whowechina/popn_pico/PCB/Popn2/3dmodels/SKSTAAE010.stp

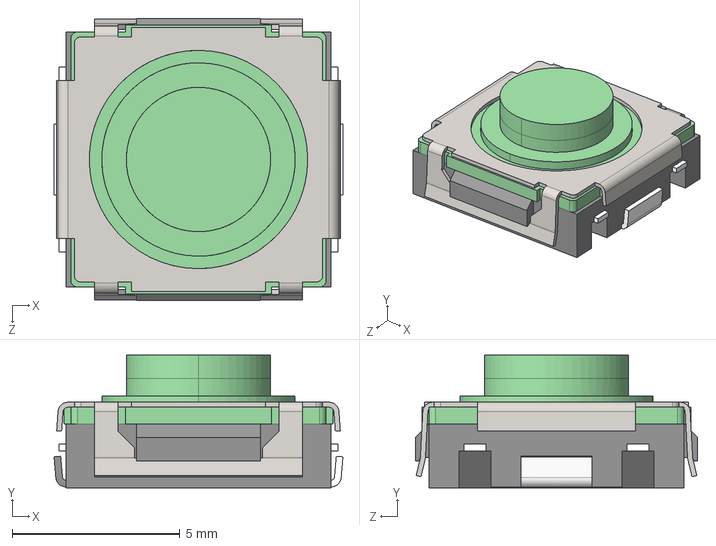
[picture p54: CAD file, 2024-12-04]
PCB/Popn2/3dmodels/SKSTAAE010.stp
8.61 x 3.95 x 8.40 mm
