whowechina/popn_pico/Production/3DPrint/popn_pico2_support.stl

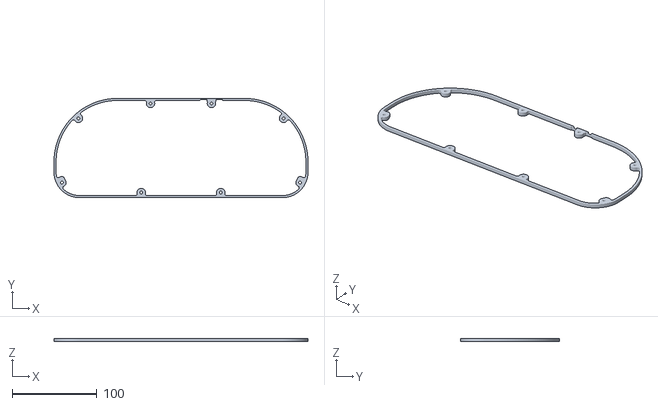
[picture p55: CAD file, 2025-01-06]
Production/3DPrint/popn_pico2_support.stl
300.3 x 117.3 x 4.00
