whowechina/popn_pico/PCB/Popn2/3dmodels/SPEAKER_SMD_1340.STEP

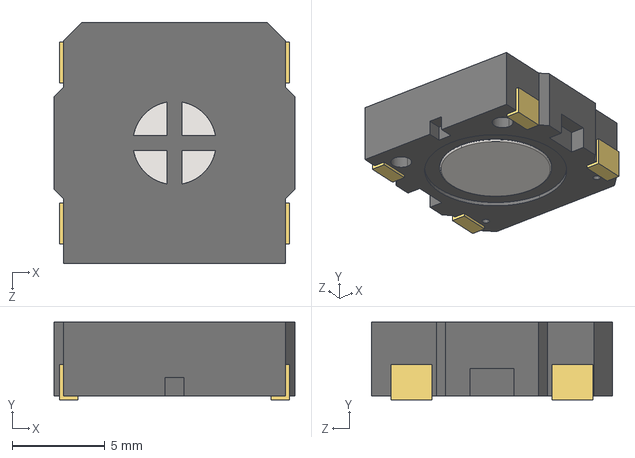
[picture p56: CAD file, 2024-12-04]
PCB/Popn2/3dmodels/SPEAKER_SMD_1340.STEP
13.0 x 4.20 x 13.0 mm
