whowechina/popn_pico/PCB/Popn2/3dmodels/User Library-WS2812-2020.step

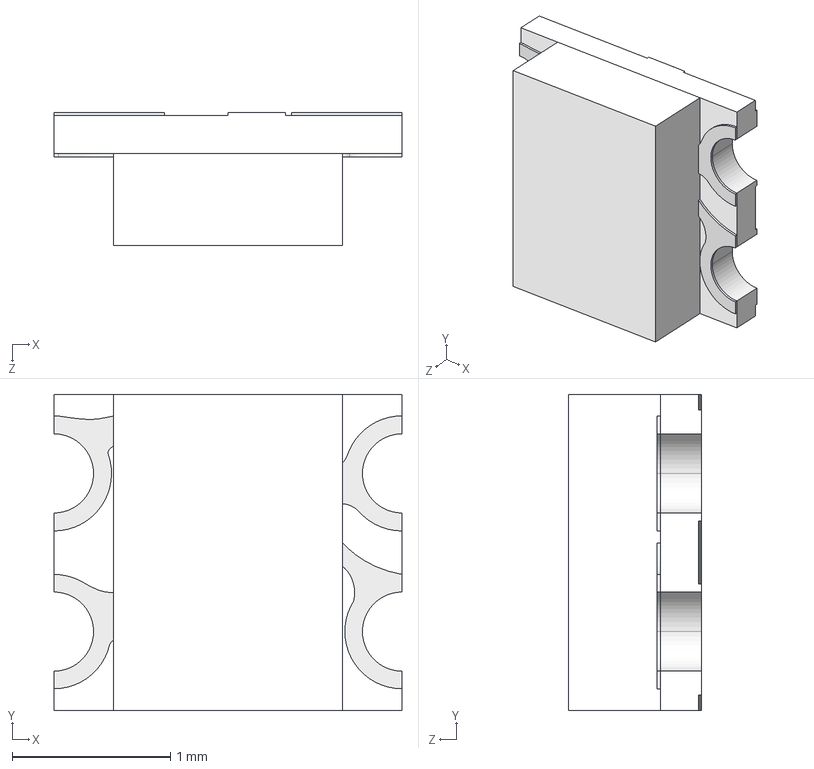
[picture p57: CAD file, 2024-12-04]
PCB/Popn2/3dmodels/User Library-WS2812-2020.step
2.20 x 2.00 x 0.84 mm
