whowechina/popn_pico/Production/3DPrint/popn_pico2_button_seat.stl

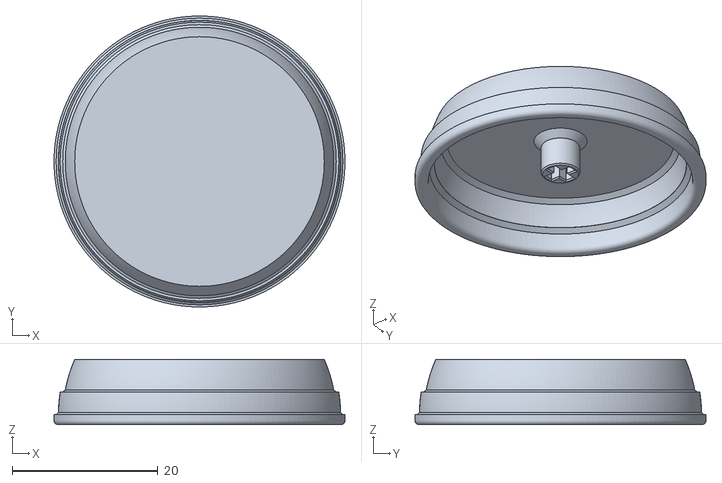
[picture p58: CAD file, 2025-01-06]
Production/3DPrint/popn_pico2_button_seat.stl
40.0 x 40.0 x 9.00
