whowechina/popn_pico/PCB/Popn2/3dmodels/SW-DTSA-63K-V.stp

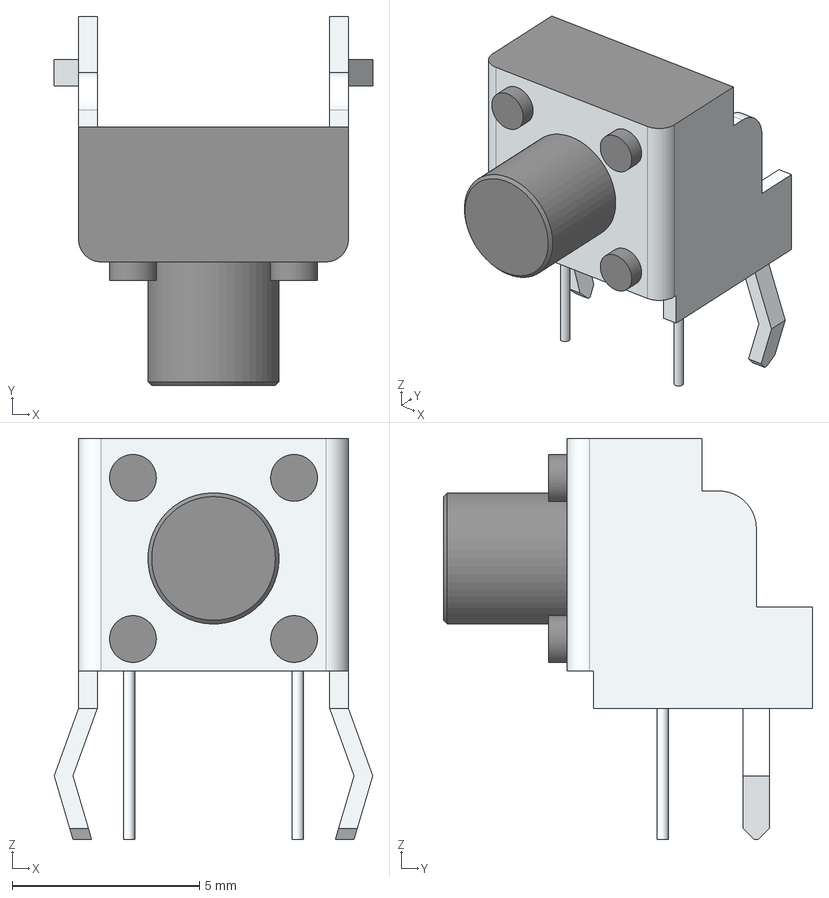
[picture p59: CAD file, 2024-12-04]
PCB/Popn2/3dmodels/SW-DTSA-63K-V.stp
8.50 x 9.85 x 10.7 mm
