whowechina/popn_pico/PCB/Popn2/3dmodels/pn5180.step

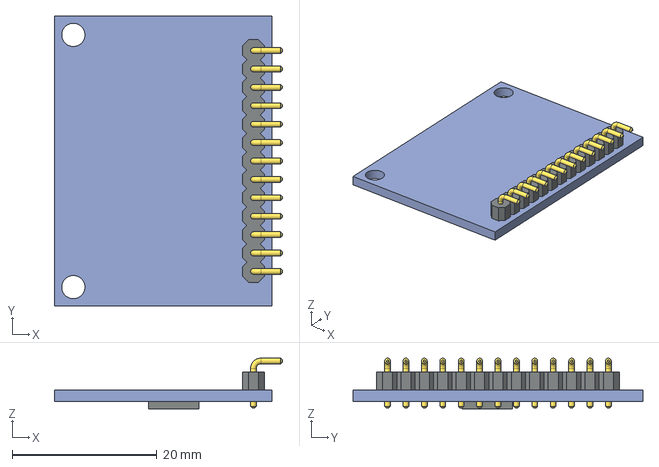
[picture p60: CAD file, 2024-12-04]
PCB/Popn2/3dmodels/pn5180.step
31.5 x 40.0 x 7.00 mm
