whowechina/popn_pico/PCB/Popn2/3dmodels/Slider.step

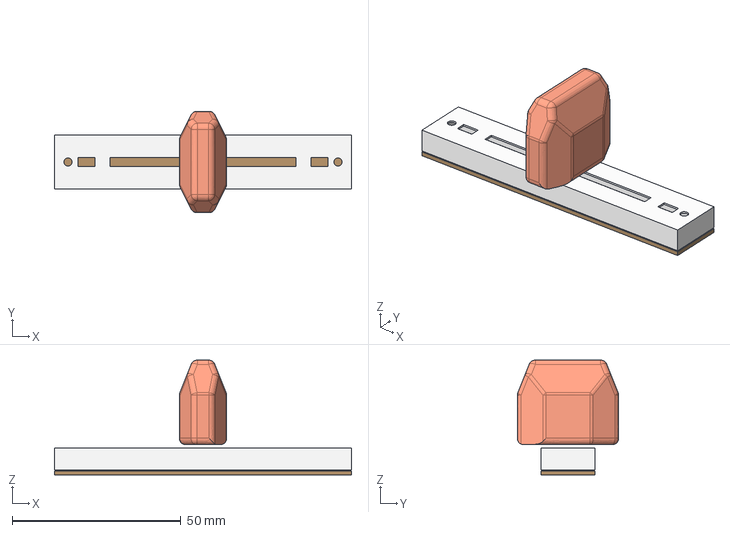
[picture p61: CAD file, 2024-12-04]
PCB/Popn2/3dmodels/Slider.step
88.0 x 30.0 x 34.0 mm
