whowechina/popn_pico/PCB/Popn2/3dmodels/Magnetic Pogo Connector 5 Pin (M) - 副本.STEP

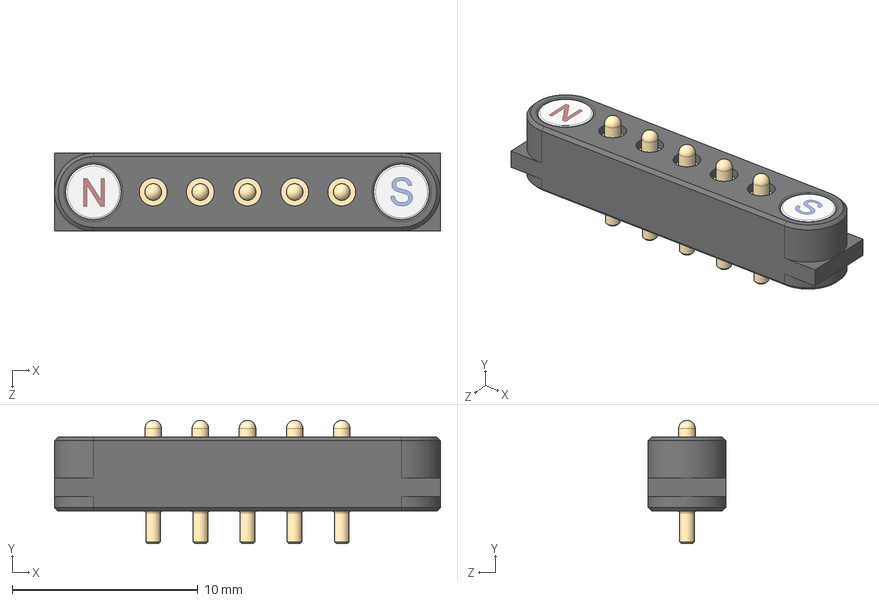
[picture p62: CAD file, 2024-12-04]
PCB/Popn2/3dmodels/Magnetic Pogo Connector 5 Pin (M) - 副本.STEP
20.8 x 6.65 x 4.20 mm
