whowechina/popn_pico/PCB/Popn2/3dmodels/SM04B-SRSS-TB.STEP

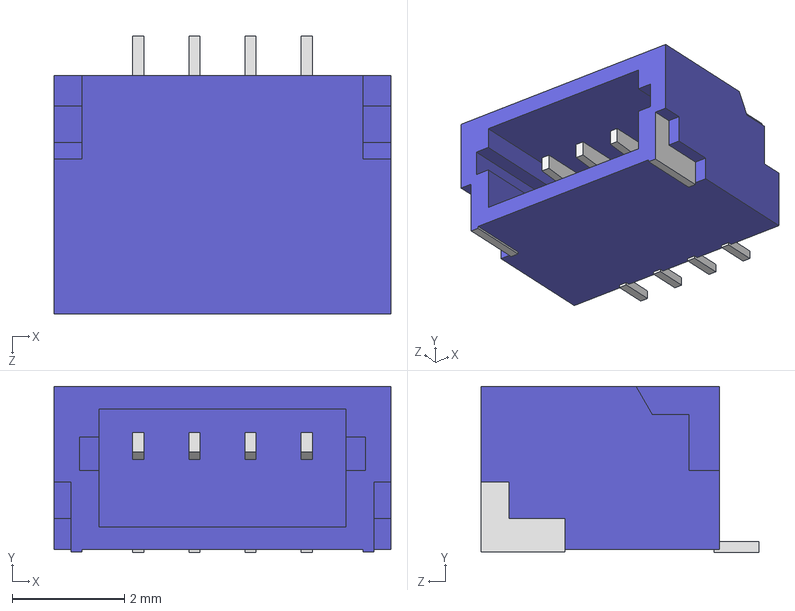
[picture p63: CAD file, 2024-12-04]
PCB/Popn2/3dmodels/SM04B-SRSS-TB.STEP
6.00 x 2.96 x 4.95 mm
