whowechina/popn_pico/PCB/Popn2/3dmodels/Kailh_PG1353.STEP

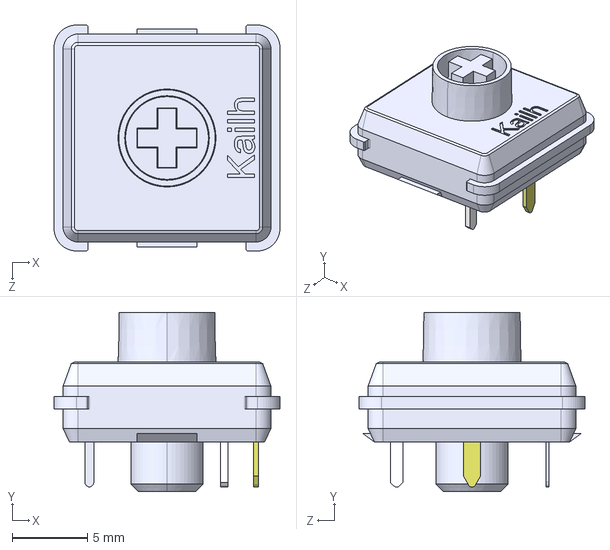
[picture p64: CAD file, 2024-12-04]
PCB/Popn2/3dmodels/Kailh_PG1353.STEP
15.0 x 11.9 x 15.0 mm
