whowechina/popn_pico/PCB/Popn2/3dmodels/Kailh Polia.step

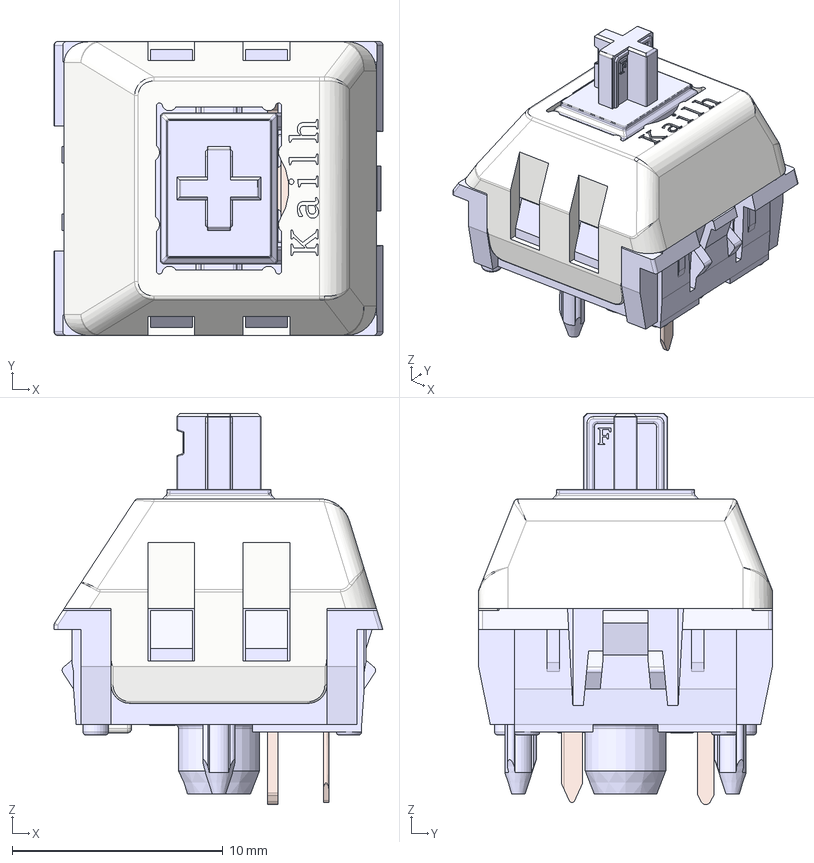
[picture p65: CAD file, 2024-12-04]
PCB/Popn2/3dmodels/Kailh Polia.step
15.6 x 14.0 x 18.5 mm
Housing
ThickContact
SpringContact
Stem
Lid
