whowechina/popn_pico/PCB/Popn2/3dmodels/mpr121_breakout_v13.stl

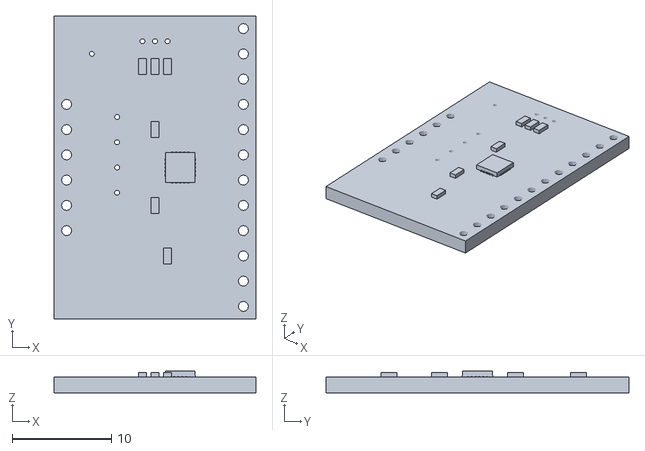
[picture p67: CAD file, 2024-12-04]
PCB/Popn2/3dmodels/mpr121_breakout_v13.stl
20.3 x 30.5 x 2.20
