whowechina/popn_pico/PCB/Popn2/3dmodels/SMD WS2812B-3535.step

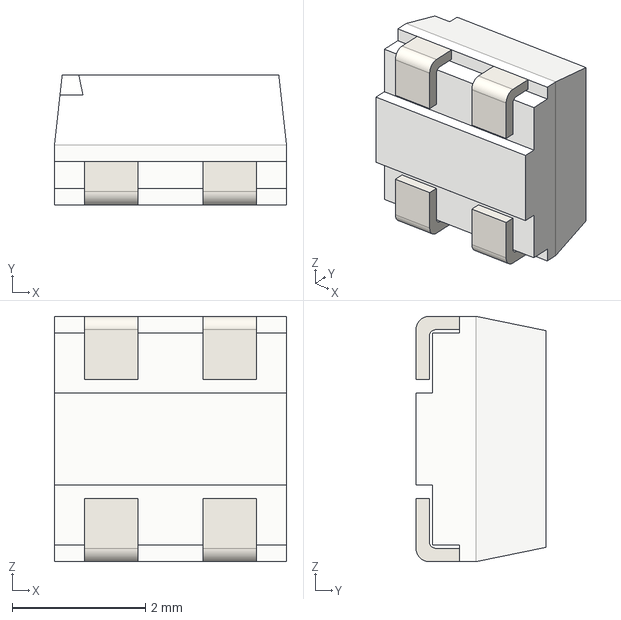
[picture p68: CAD file, 2024-12-04]
PCB/Popn2/3dmodels/SMD WS2812B-3535.step
3.48 x 1.95 x 3.68 mm
