whowechina/popn_pico/PCB/Popn2/3dmodels/User Library-RGB1204.STEP

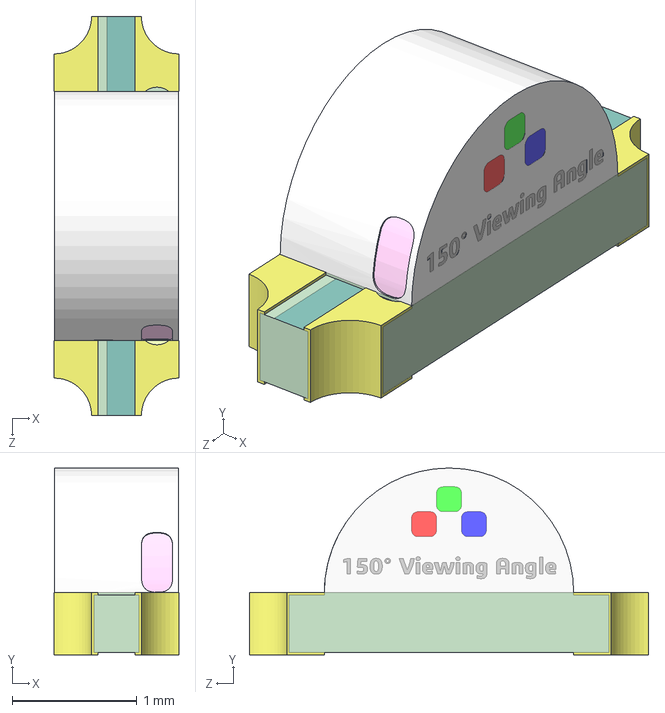
[picture p69: CAD file, 2024-12-04]
PCB/Popn2/3dmodels/User Library-RGB1204.STEP
1.00 x 1.50 x 3.20 mm
