whowechina/popn_pico/PCB/Popn2/3dmodels/geki_button.step

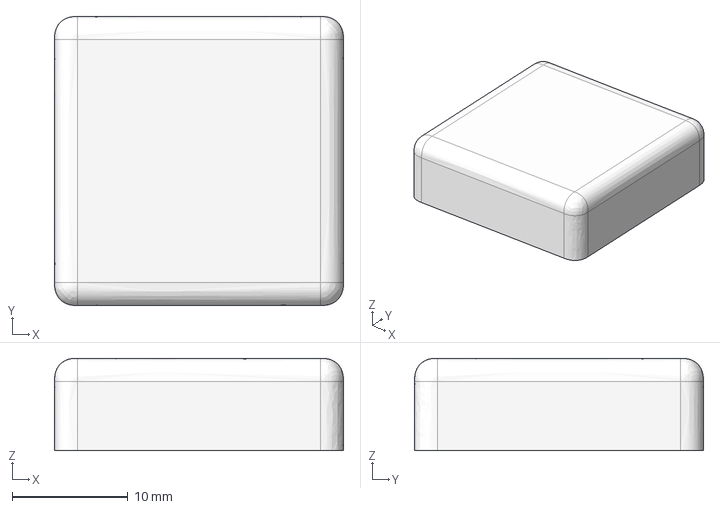
[picture p70: CAD file, 2024-12-04]
PCB/Popn2/3dmodels/geki_button.step
25.0 x 25.0 x 8.00 mm
