whowechina/popn_pico/PCB/Popn2/3dmodels/SKRRABE010.stp

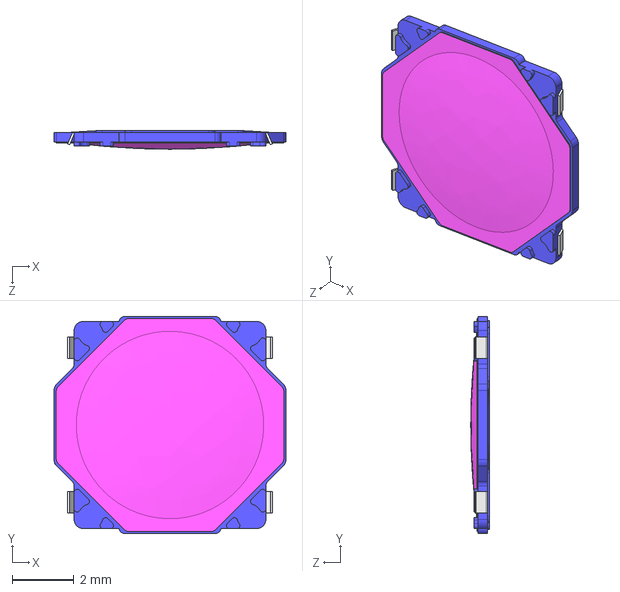
[picture p71: CAD file, 2024-12-04]
PCB/Popn2/3dmodels/SKRRABE010.stp
7.50 x 7.03 x 0.6 mm
