whowechina/popn_pico/PCB/Popn2/3dmodels/Button Cap.step

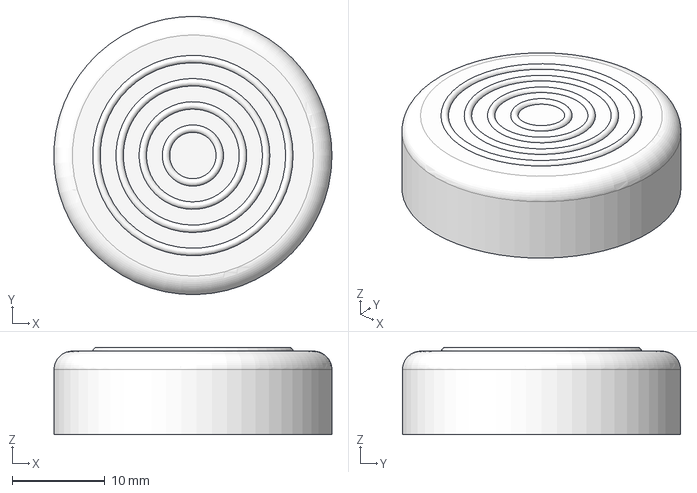
[picture p72: CAD file, 2024-12-04]
PCB/Popn2/3dmodels/Button Cap.step
30.0 x 30.0 x 9.40 mm
