whowechina/popn_pico/PCB/Popn2/3dmodels/dcdc_3to5.step

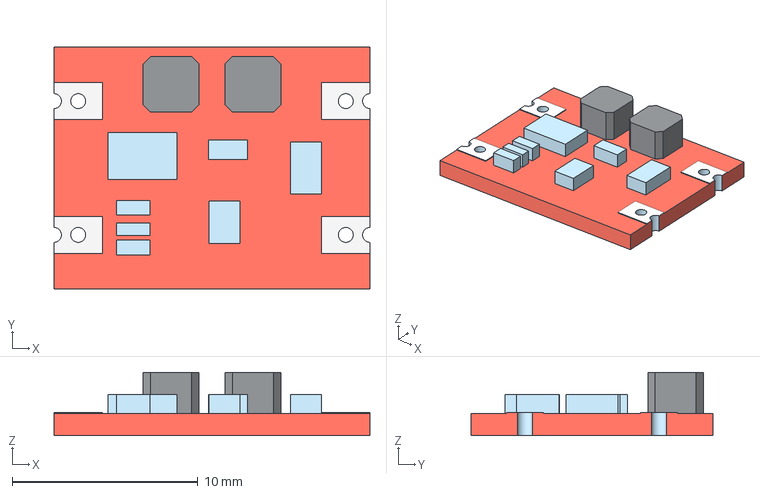
[picture p73: CAD file, 2024-12-04]
PCB/Popn2/3dmodels/dcdc_3to5.step
17.0 x 13.0 x 3.40 mm
