whowechina/popn_pico/PCB/Popn2/3dmodels/SS49E.step

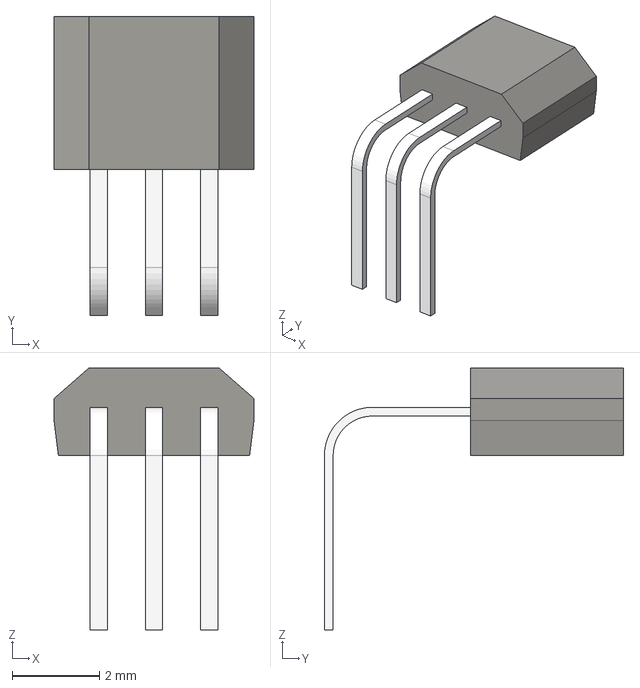
[picture p74: CAD file, 2024-12-04]
PCB/Popn2/3dmodels/SS49E.step
4.58 x 6.85 x 6.00 mm
