whowechina/popn_pico/PCB/Popn2/3dmodels/User Library-WS2812-4020.step

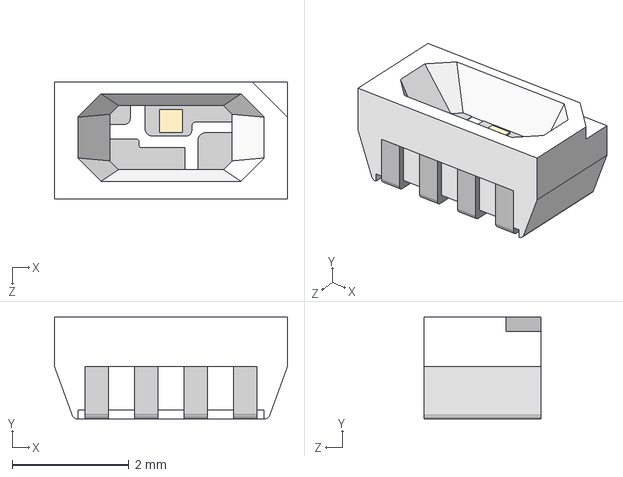
[picture p75: CAD file, 2024-12-04]
PCB/Popn2/3dmodels/User Library-WS2812-4020.step
4.00 x 1.75 x 2.00 mm
