whowechina/popn_pico/PCB/Popn2/3dmodels/SW_Hotswap_Kailh_Choc_V1.stp

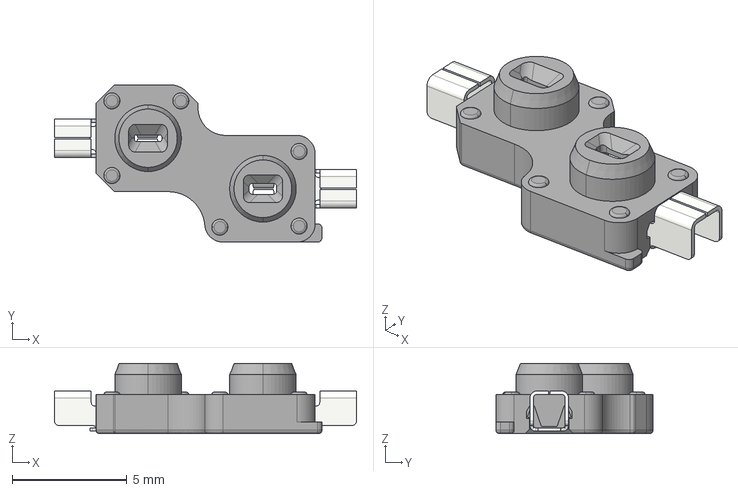
[picture p76: CAD file, 2024-12-04]
PCB/Popn2/3dmodels/SW_Hotswap_Kailh_Choc_V1.stp
13.2 x 6.85 x 3.05 mm
