whowechina/popn_pico/PCB/Popn2/3dmodels/TRS Jack PJ-313.stp

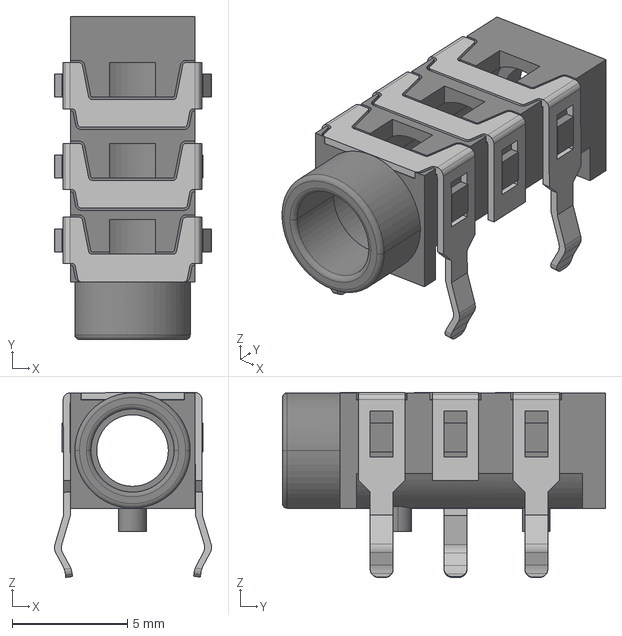
[picture p77: CAD file, 2024-12-04]
PCB/Popn2/3dmodels/TRS Jack PJ-313.stp
6.81 x 14.0 x 8.02 mm
