whowechina/popn_pico/PCB/Popn2/3dmodels/WS2812-2020.STEP

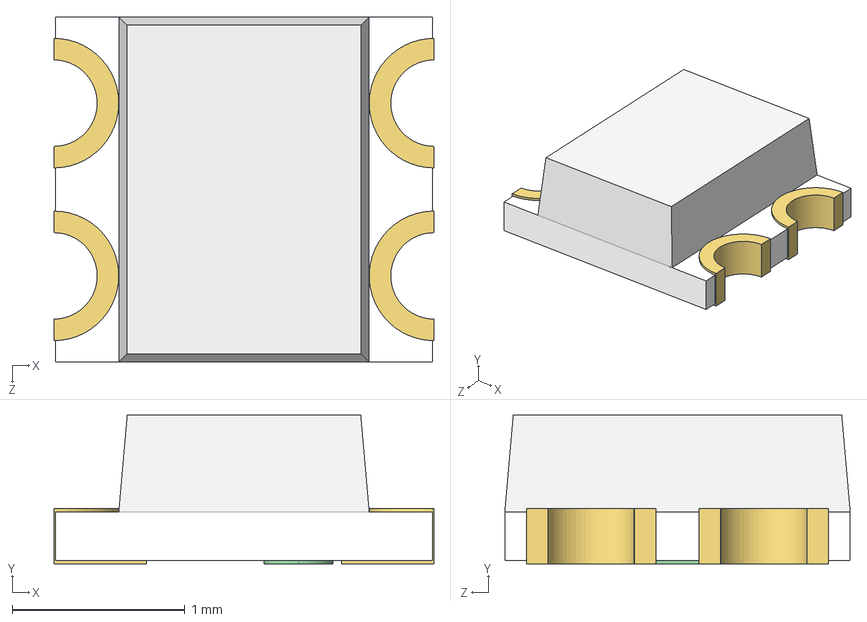
[picture p78: CAD file, 2024-12-04]
PCB/Popn2/3dmodels/WS2812-2020.STEP
2.20 x 0.86 x 2.00 mm
