whowechina/popn_pico/PCB/Popn2/3dmodels/keypad_lgp.3mf

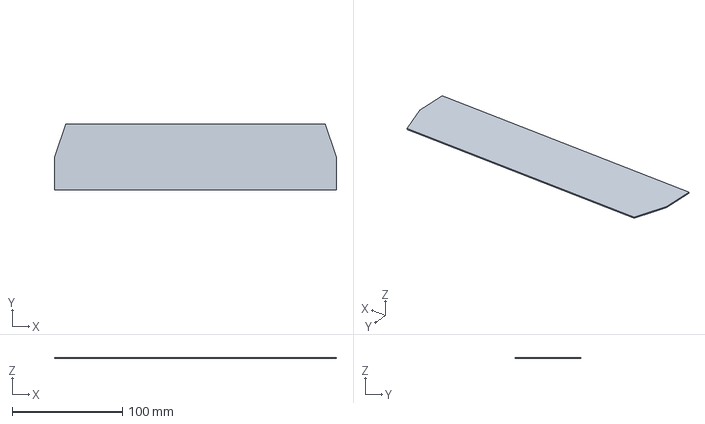
[picture p79: CAD file, 2024-12-04]
PCB/Popn2/3dmodels/keypad_lgp.3mf
256.0 x 60.0 x 1.00 mm
