whowechina/popn_pico/PCB/Popn2/3dmodels/chu_keypad_lgp.step

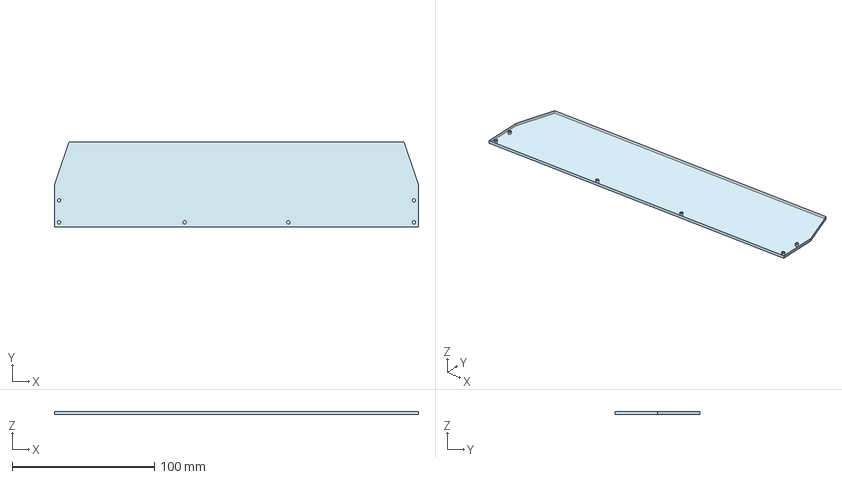
[picture p80: CAD file, 2024-12-04]
PCB/Popn2/3dmodels/chu_keypad_lgp.step
256.0 x 60.0 x 2.00 mm
