whowechina/popn_pico/PCB/Popn2/3dmodels/EVQ-P1D05M.stp

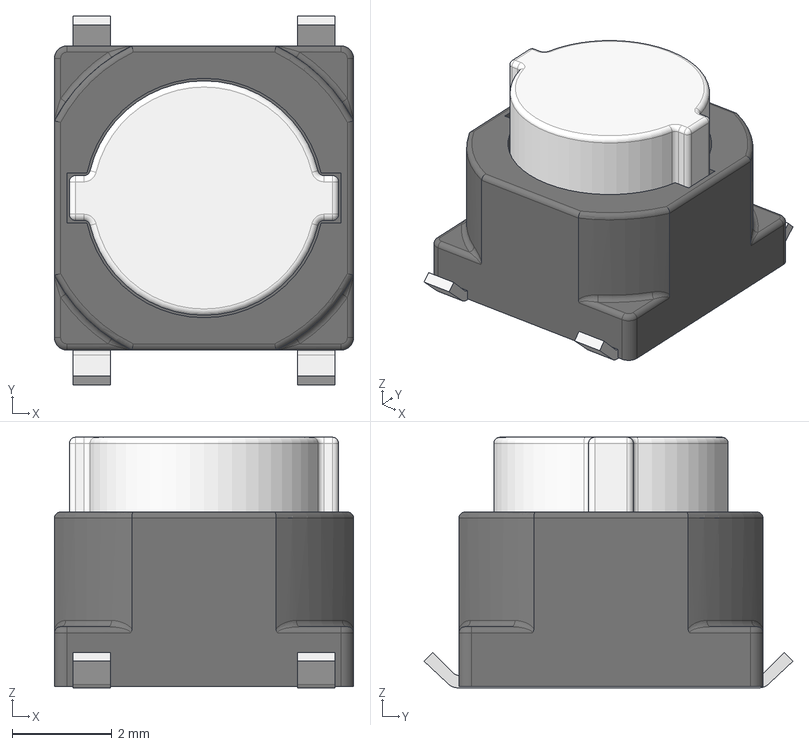
[picture p81: CAD file, 2024-12-04]
PCB/Popn2/3dmodels/EVQ-P1D05M.stp
6.00 x 7.40 x 5.03 mm
