whowechina/popn_pico/PCB/Popn2/3dmodels/8002A.step

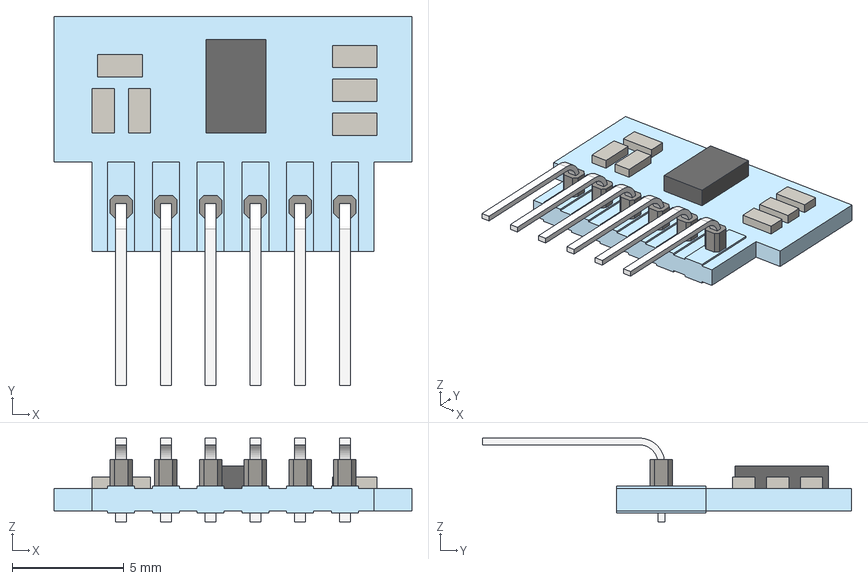
[picture p82: CAD file, 2024-12-04]
PCB/Popn2/3dmodels/8002A.step
16.0 x 16.5 x 3.75 mm
