whowechina/popn_pico/PCB/Popn2/3dmodels/User Library-PTS645SL95SMTR92-LFS.STEP

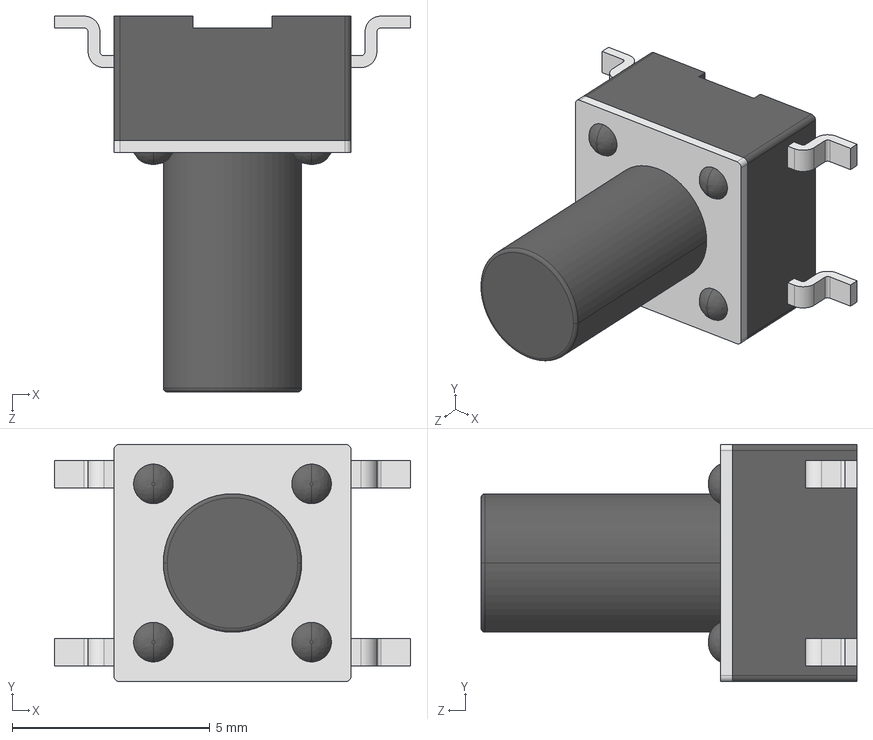
[picture p83: CAD file, 2024-12-04]
PCB/Popn2/3dmodels/User Library-PTS645SL95SMTR92-LFS.STEP
9.00 x 6.00 x 9.50 mm
