whowechina/popn_pico/PCB/Popn2/3dmodels/Magnetic Pogo Connector 5 Pin (Type 4).STEP

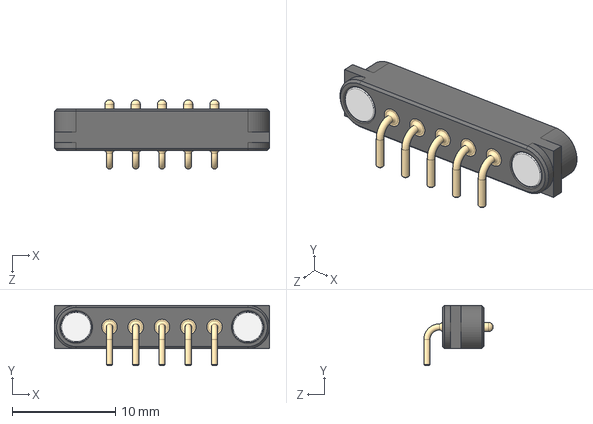
[picture p84: CAD file, 2024-12-04]
PCB/Popn2/3dmodels/Magnetic Pogo Connector 5 Pin (Type 4).STEP
20.8 x 5.85 x 6.70 mm
