whowechina/popn_pico/PCB/Popn2/3dmodels/WS2812-0807.STEP

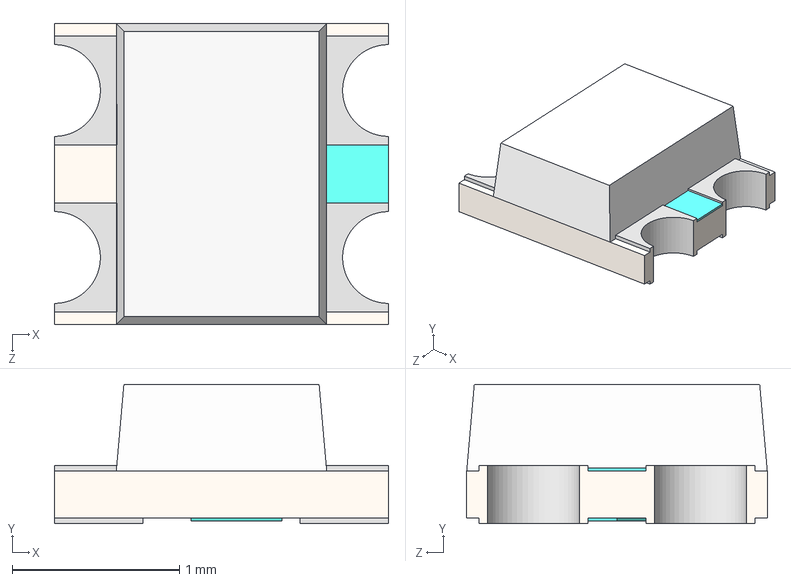
[picture p85: CAD file, 2024-12-04]
PCB/Popn2/3dmodels/WS2812-0807.STEP
2.00 x 0.835 x 1.80 mm
