whowechina/popn_pico/PCB/Popn2/3dmodels/Geki_Slider.step

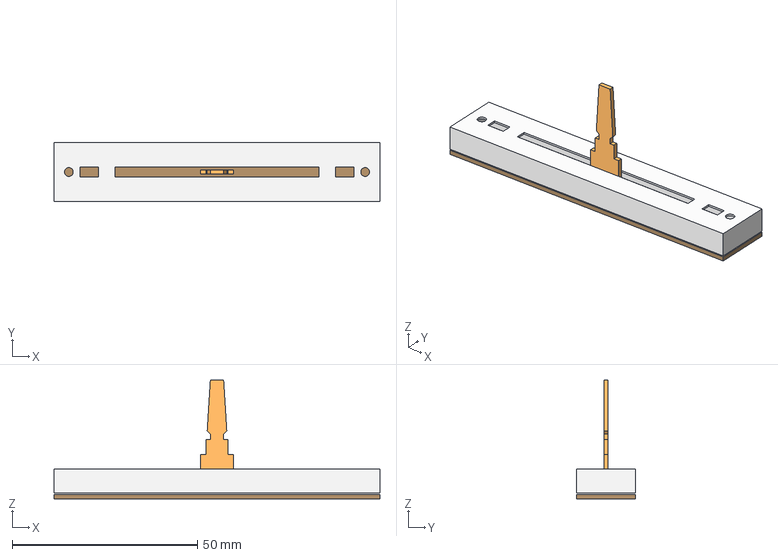
[picture p86: CAD file, 2024-12-04]
PCB/Popn2/3dmodels/Geki_Slider.step
88.0 x 16.0 x 32.0 mm
