whowechina/popn_pico/PCB/Popn2/3dmodels/SW_Kailh_Choc_V1.stp

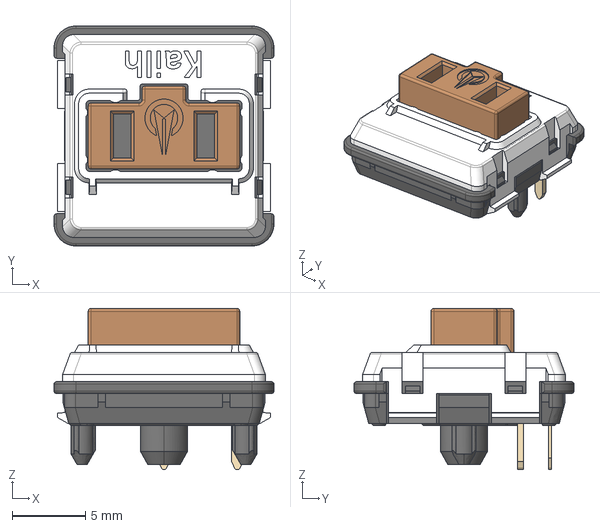
[picture p87: CAD file, 2024-12-04]
PCB/Popn2/3dmodels/SW_Kailh_Choc_V1.stp
15.0 x 15.0 x 11.0 mm
