whowechina/popn_pico/PCB/Popn2/3dmodels/LED_WS2812_2020.step

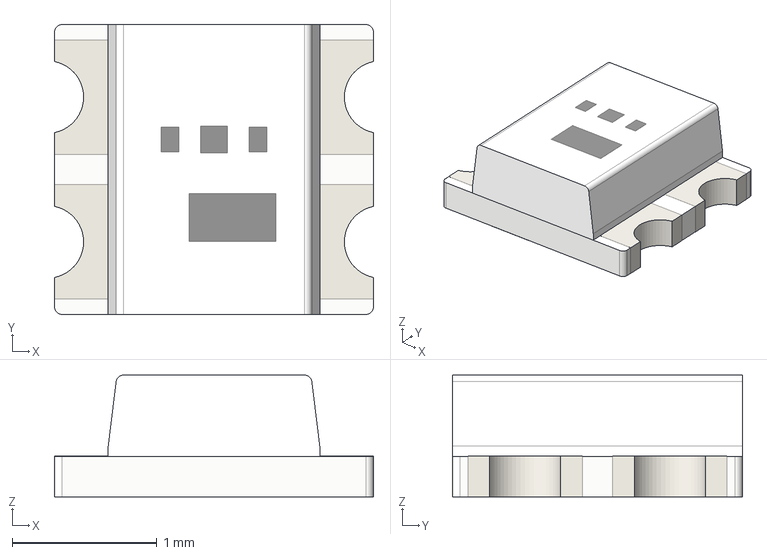
[picture p88: CAD file, 2024-12-04]
PCB/Popn2/3dmodels/LED_WS2812_2020.step
2.20 x 2.00 x 0.842 mm
