whowechina/popn_pico/PCB/Popn2/3dmodels/Magnetic Pogo Connector 5 Pin (Type 3).STEP

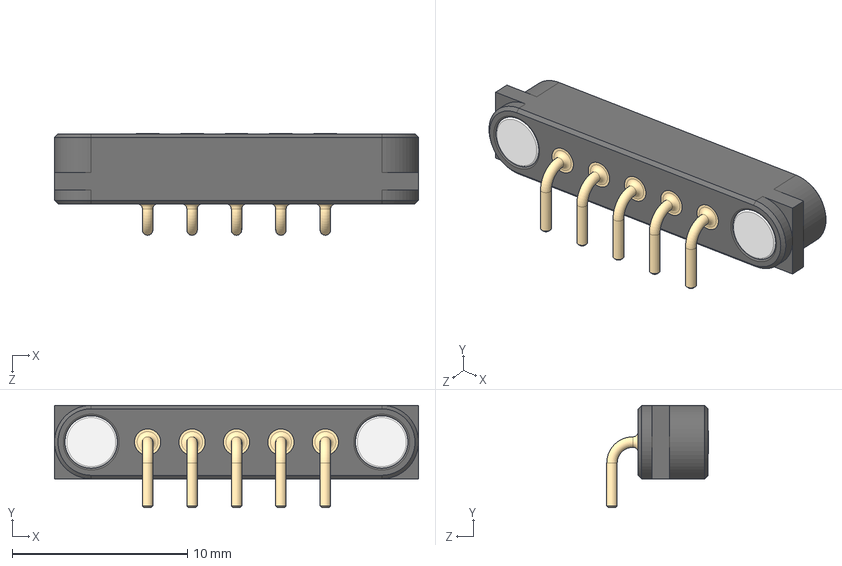
[picture p89: CAD file, 2024-12-04]
PCB/Popn2/3dmodels/Magnetic Pogo Connector 5 Pin (Type 3).STEP
20.8 x 5.85 x 5.80 mm
