whowechina/popn_pico/PCB/Popn2/3dmodels/gp2y0e03.3mf

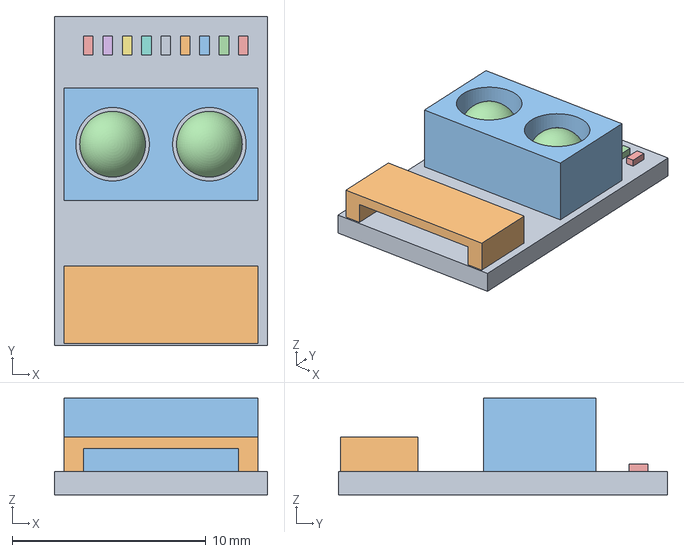
[picture p90: CAD file, 2024-12-04]
PCB/Popn2/3dmodels/gp2y0e03.3mf
11.0 x 17.0 x 5.00 mm
