whowechina/popn_pico/PCB/Popn2/3dmodels/J 2835.step

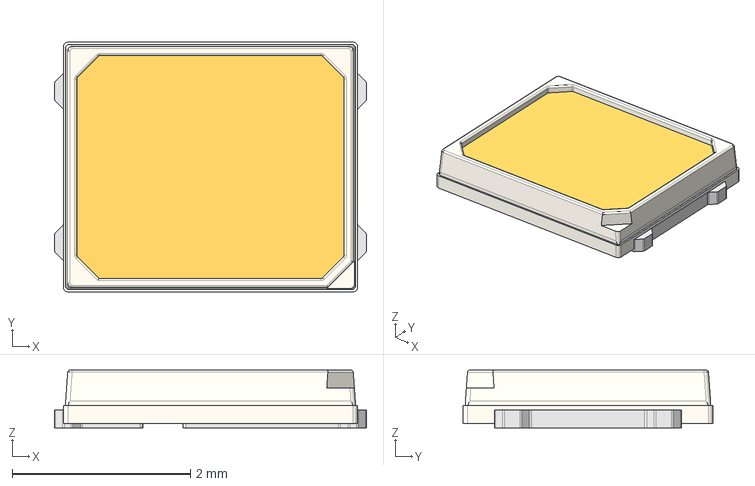
[picture p91: CAD file, 2022-08-22]
PCB/Popn2/3dmodels/J 2835.step
3.50 x 2.80 x 0.65 mm
