whowechina/popn_pico/PCB/Popn2/3dmodels/Tact Switch 4.5mm SMT.step

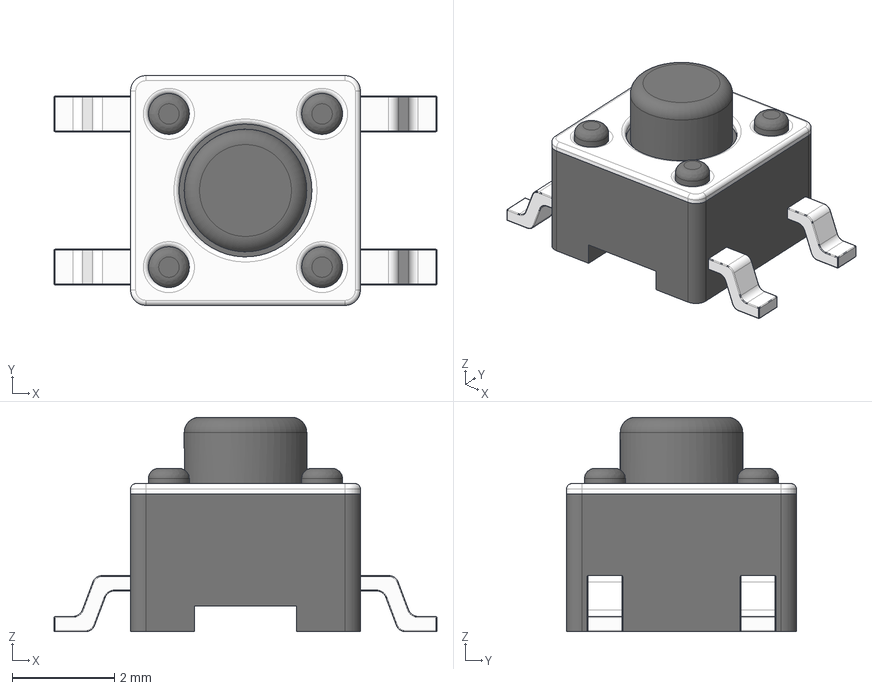
[picture p92: CAD file, 2022-08-22]
PCB/Popn2/3dmodels/Tact Switch 4.5mm SMT.step
7.50 x 4.50 x 4.20 mm
